mattjfan/holonomic-plant-pot/cad/omni_wheel_cover_out.sl.stl

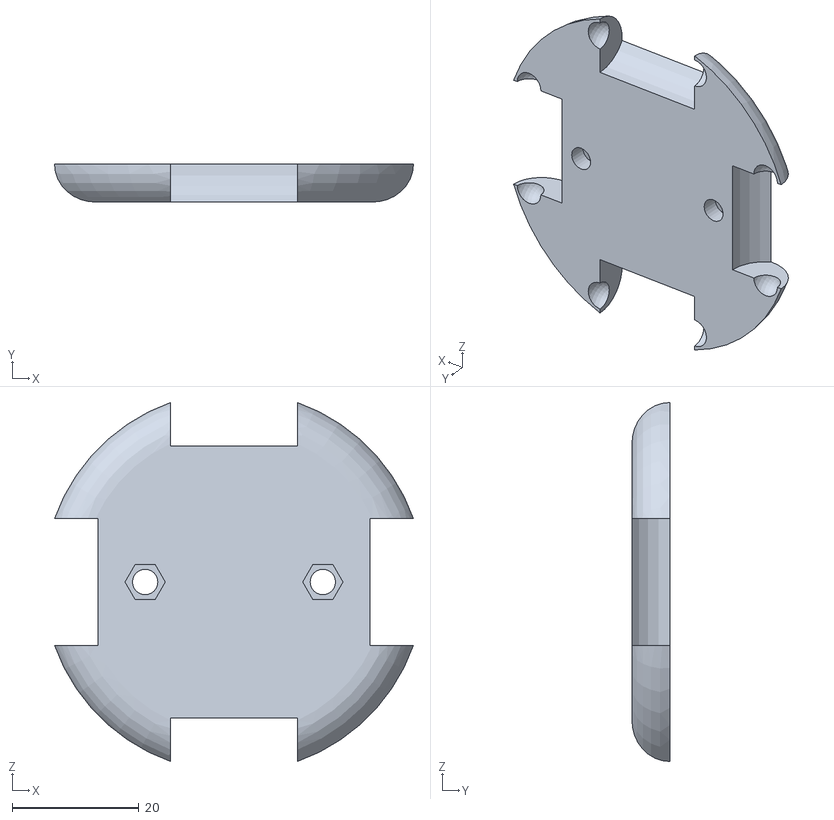
[picture p16: CAD file, 2018-10-30]
cad/omni_wheel_cover_out.sl.stl
56.6 x 6.00 x 56.6
