mattjfan/holonomic-plant-pot/cad/omni_wheel_v2/omni_roller_v2.stl

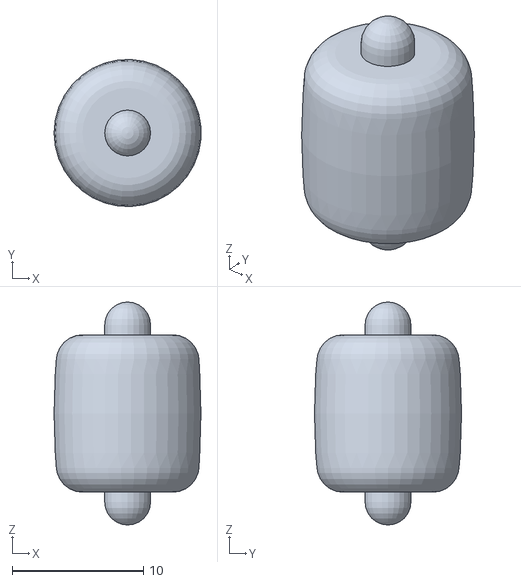
[picture p17: CAD file, 2018-10-30, an earlier design]
cad/omni_wheel_v2/omni_roller_v2.stl
11.2 x 11.2 x 17.0
