mattjfan/holonomic-plant-pot/cad/omni_wheel_v2/omni_wheel_cover_out.stl

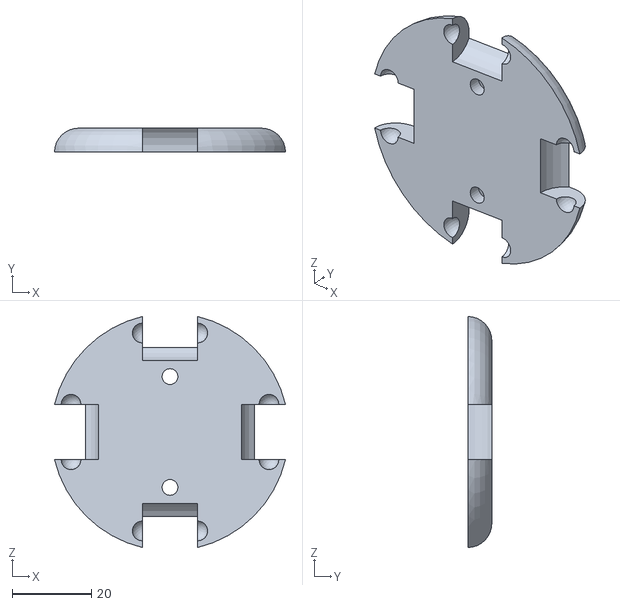
[picture p18: CAD file, 2018-10-30, an earlier design]
cad/omni_wheel_v2/omni_wheel_cover_out.stl
58.3 x 6.00 x 58.3
